MrWyss/ha-assist-mic-satellite/code/esphome/media/animation/micsatellite_init.png

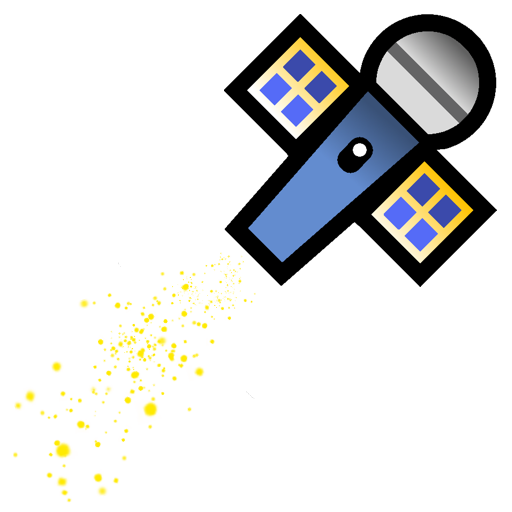
code/esphome/media/animation/micsatellite_init.png
