MrWyss/ha-assist-mic-satellite/code/esphome/media/animation/micsatellite_replying.png

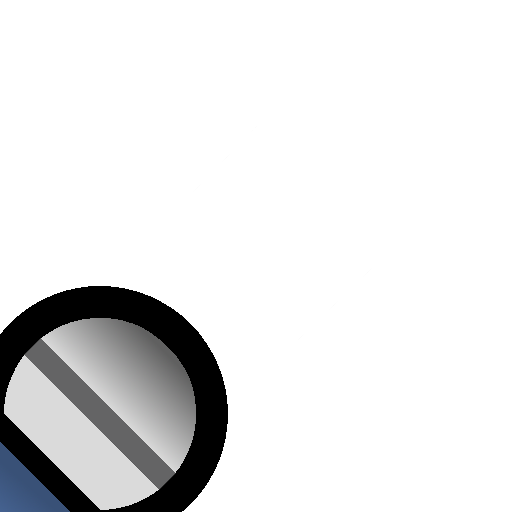
code/esphome/media/animation/micsatellite_replying.png
