MrWyss/ha-assist-mic-satellite/docs/assets/FullMic.png

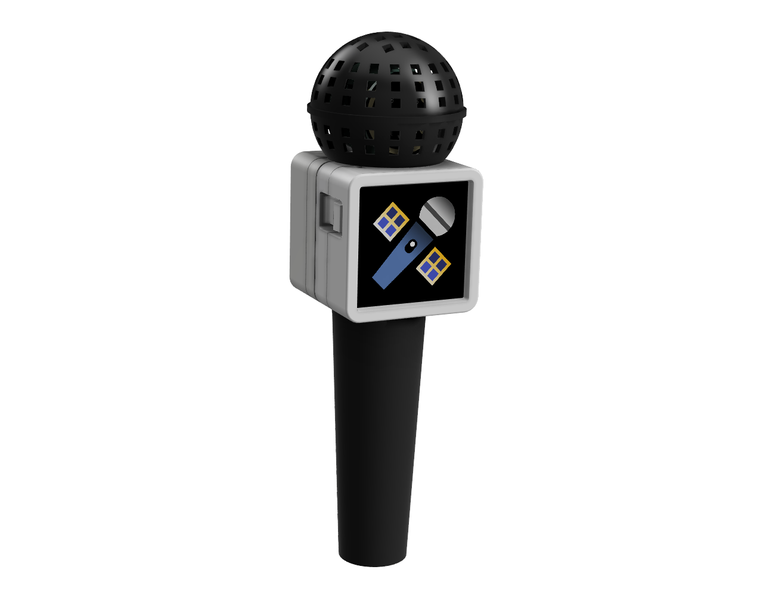
docs/assets/FullMic.png
