MrWyss/ha-assist-mic-satellite/docs/assets/HAConfig.png

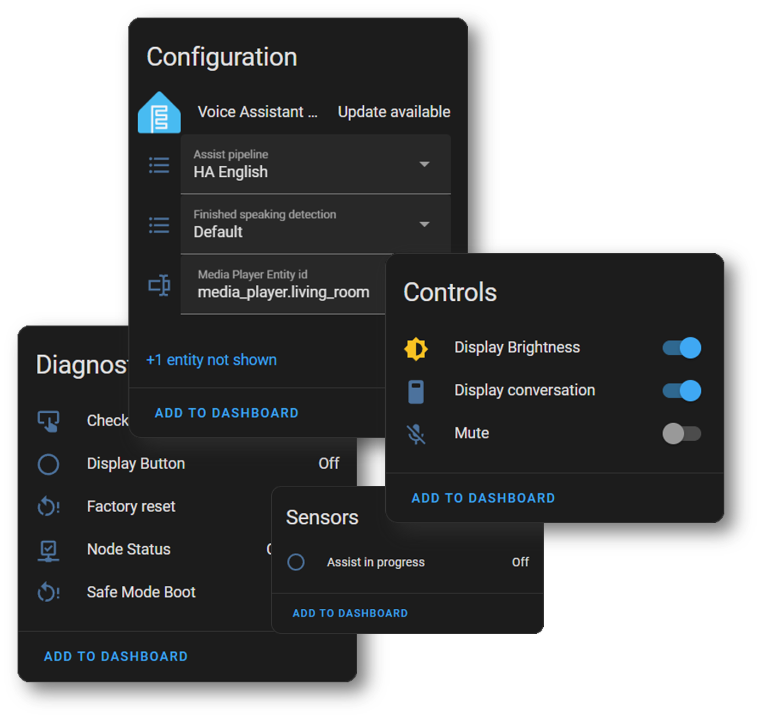
docs/assets/HAConfig.png
